AbdulMuqeet2468/SPIDER/Hardware/CAD Models/SPIDER v2/Images/3.png

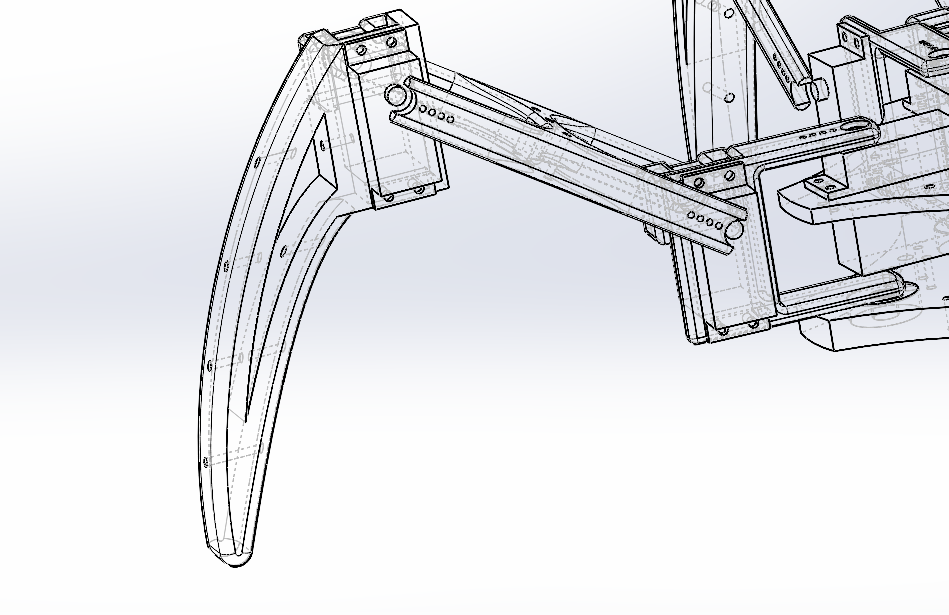
Hardware/CAD Models/SPIDER v2/Images/3.png
