AbdulMuqeet2468/SPIDER/Hardware/CAD Models/SPIDER v2/Solidworks prt files/servo motor.SLDPRT

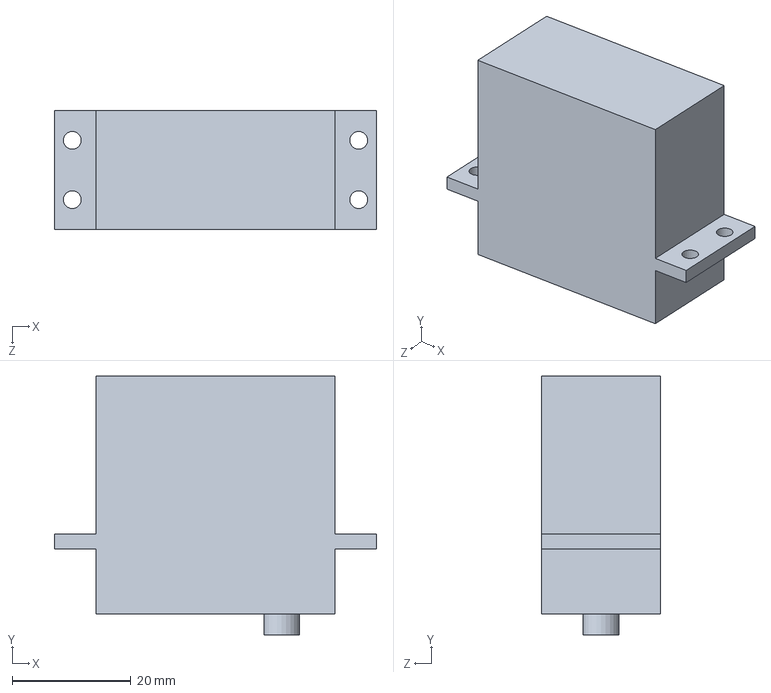
[picture p20: CAD file, 2026-06-04]
Hardware/CAD Models/SPIDER v2/Solidworks prt files/servo motor.SLDPRT
54.3 x 43.6 x 20.0 mm
