AbdulMuqeet2468/SPIDER/Hardware/CAD Models/SPIDER v2/stll files/base plate.STL

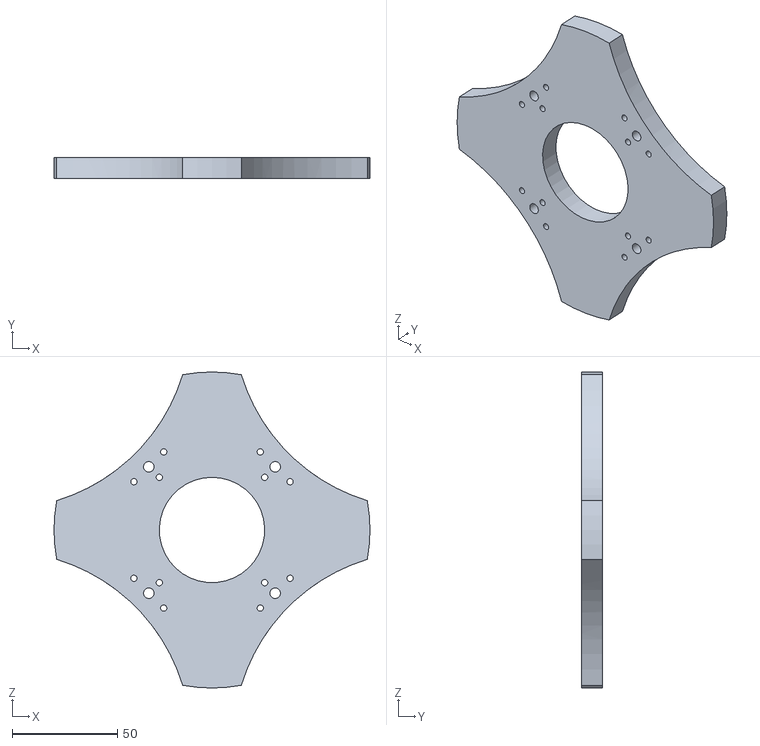
[picture p21: CAD file, 2026-06-04]
Hardware/CAD Models/SPIDER v2/stll files/base plate.STL
150.0 x 10.0 x 150.0
