AbdulMuqeet2468/SPIDER/Hardware/CAD Models/SPIDER v2/Solidworks prt files/top plate.SLDPRT

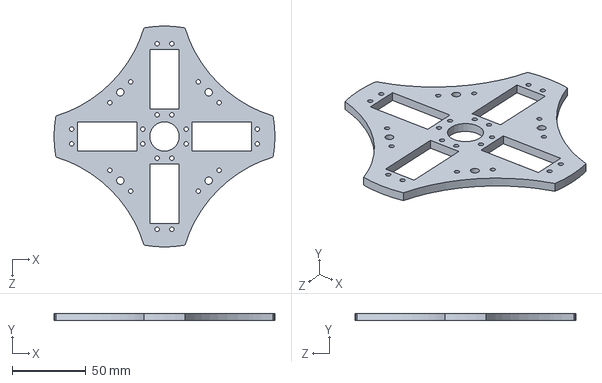
[picture p22: CAD file, 2026-06-04]
Hardware/CAD Models/SPIDER v2/Solidworks prt files/top plate.SLDPRT
150.0 x 5.00 x 150.0 mm
