AbdulMuqeet2468/SPIDER/Hardware/CAD Models/SPIDER v2/stll files/top plate_n.STL

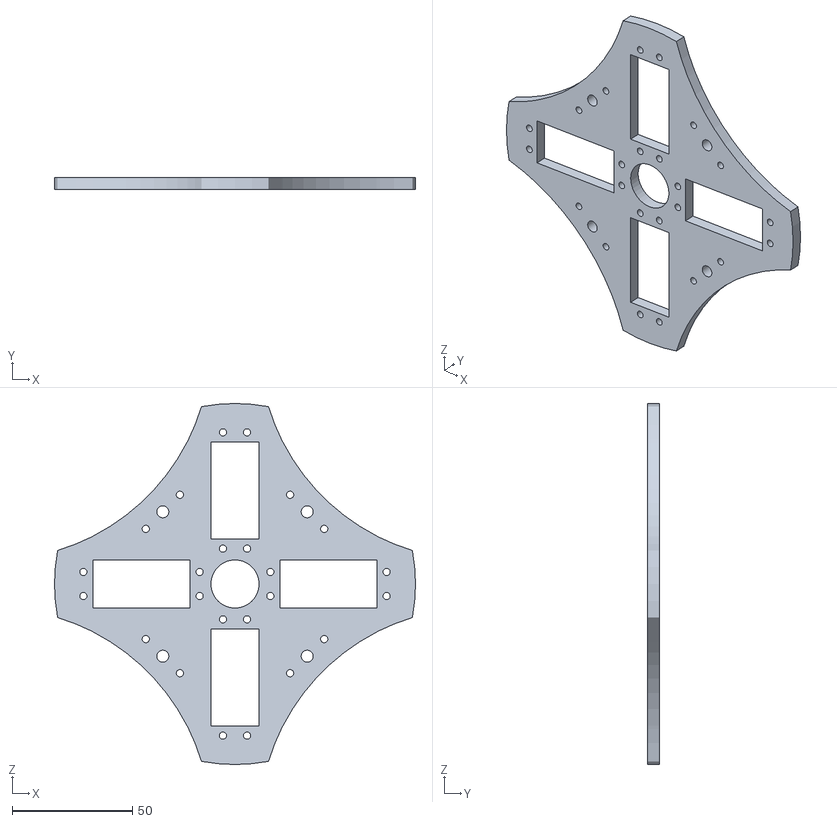
[picture p23: CAD file, 2026-06-04]
Hardware/CAD Models/SPIDER v2/stll files/top plate_n.STL
150.0 x 5.00 x 150.0
