AbdulMuqeet2468/SPIDER/Hardware/CAD Models/SPIDER v2/Solidworks prt files/femur.SLDPRT

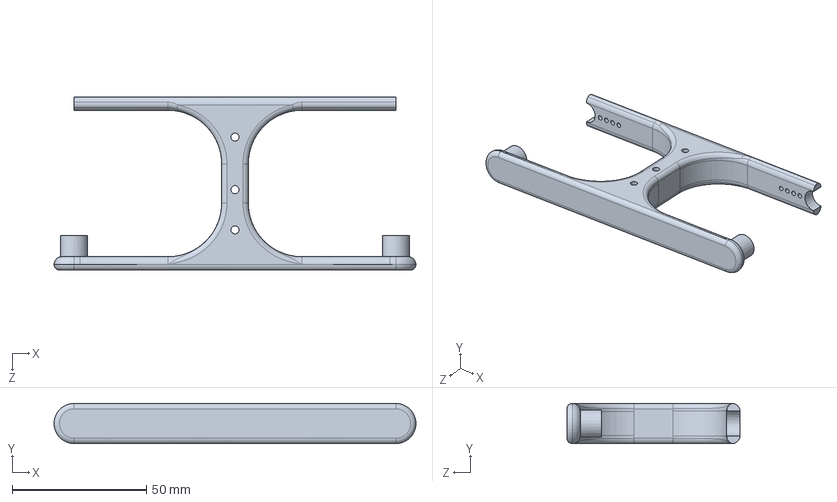
[picture p24: CAD file, 2026-06-04]
Hardware/CAD Models/SPIDER v2/Solidworks prt files/femur.SLDPRT
135.0 x 15.0 x 64.6 mm
