AbdulMuqeet2468/SPIDER/Hardware/CAD Models/SPIDER v2/stll files/coxa connector left_n.STL

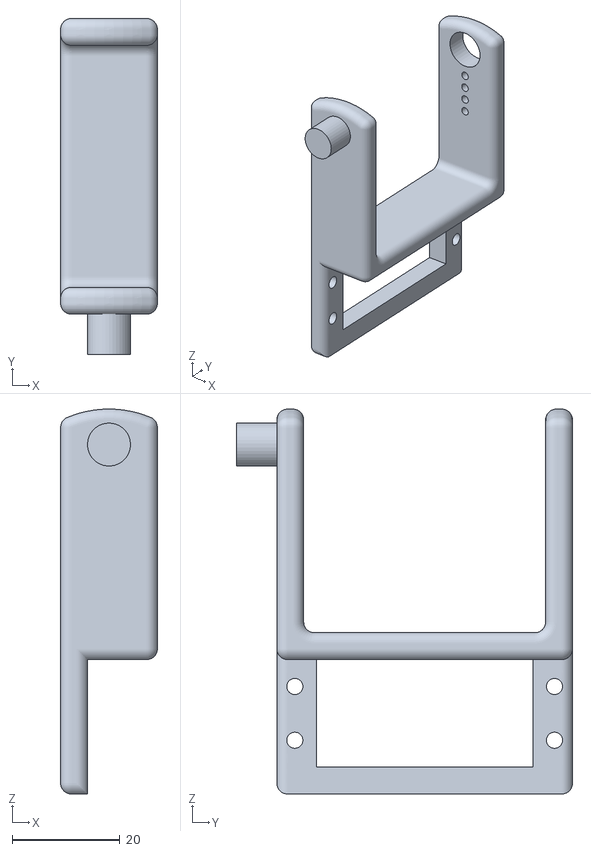
[picture p25: CAD file, 2026-06-04]
Hardware/CAD Models/SPIDER v2/stll files/coxa connector left_n.STL
18.0 x 62.5 x 71.6
