AbdulMuqeet2468/SPIDER/Hardware/CAD Models/SPIDER v2/stll files/plate.STL

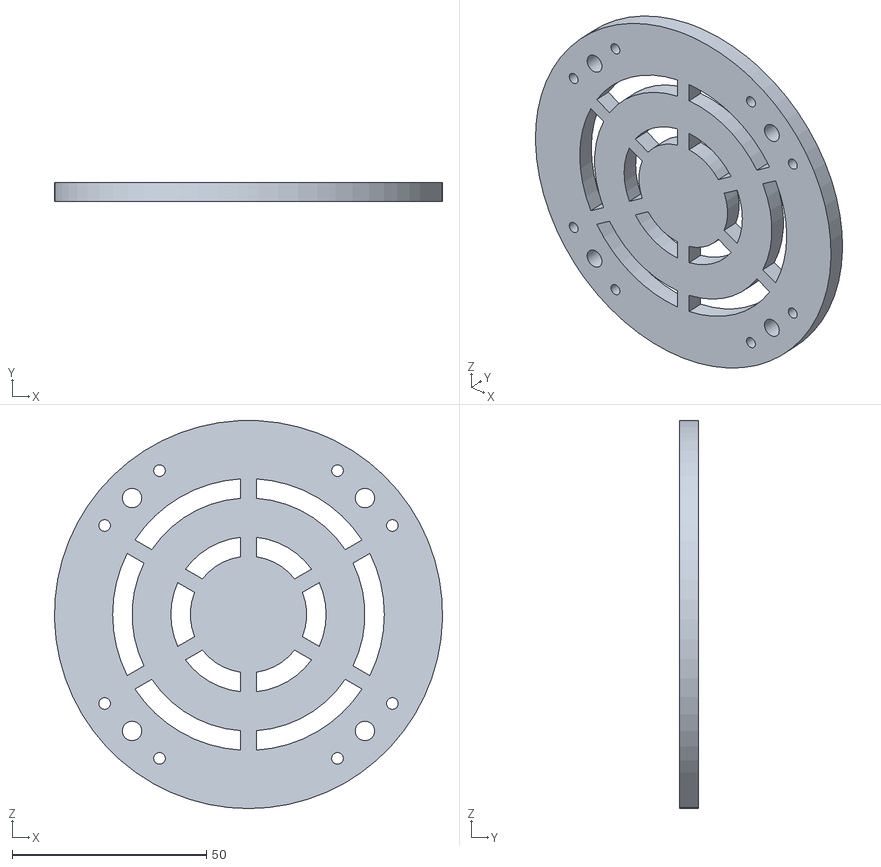
[picture p26: CAD file, 2026-06-04]
Hardware/CAD Models/SPIDER v2/stll files/plate.STL
100.0 x 5.00 x 100.0
