AbdulMuqeet2468/SPIDER/Software/Simulations/FullAsm/meshes/base_link.STL

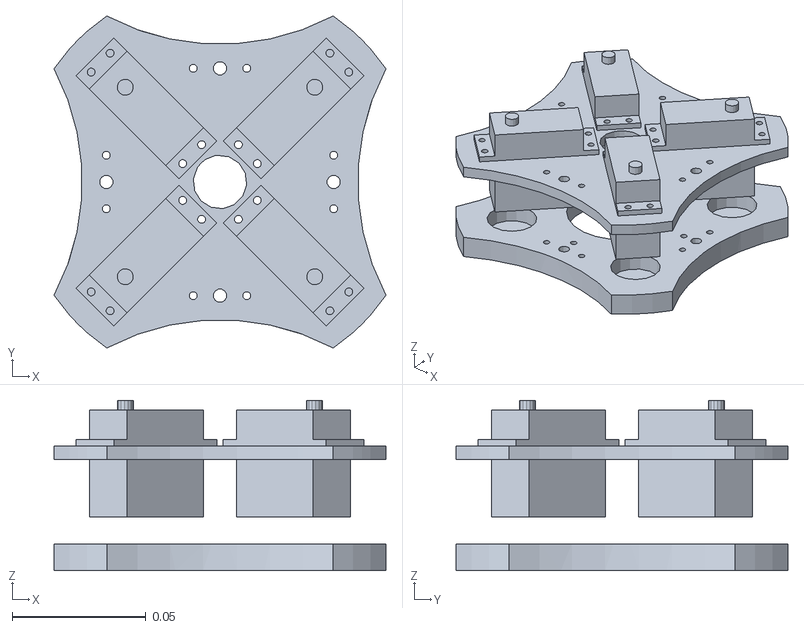
[picture p27: CAD file, 2026-06-30]
Software/Simulations/FullAsm/meshes/base_link.STL
0.124 x 0.124 x 0.0635
